cjthomas-opensource/sfx-boards/pcb-202009-9v/mech/drawings/sfx-9v-adapter.png

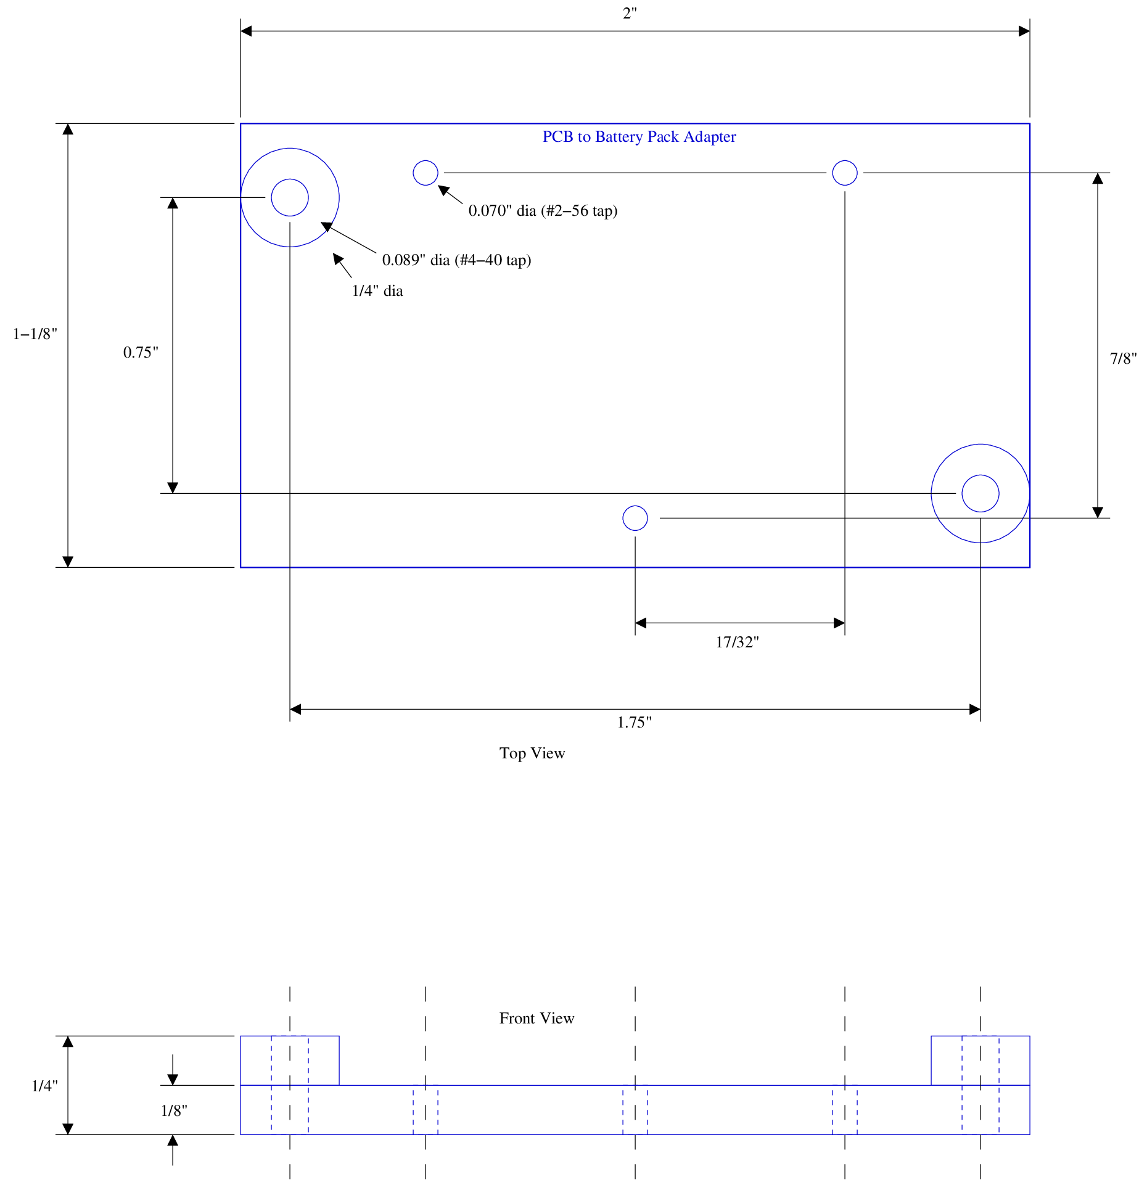
pcb-202009-9v/mech/drawings/sfx-9v-adapter.png
