cjthomas-opensource/sfx-boards/pcb-202009-9v/mech/drawings/sfx-9v-drawing.png

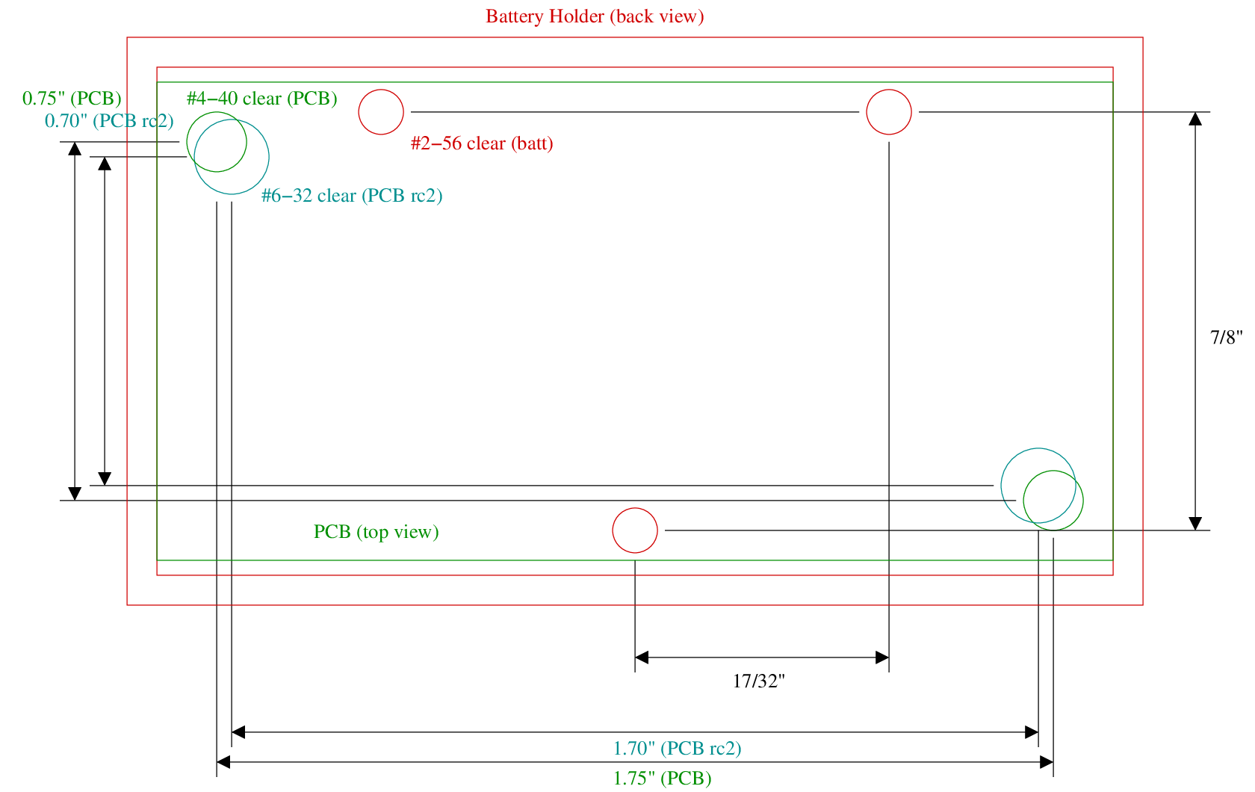
pcb-202009-9v/mech/drawings/sfx-9v-drawing.png
