cjthomas-opensource/sfx-boards/pcb-202009-9v/plots/sfx-9v-202009-rc1.png

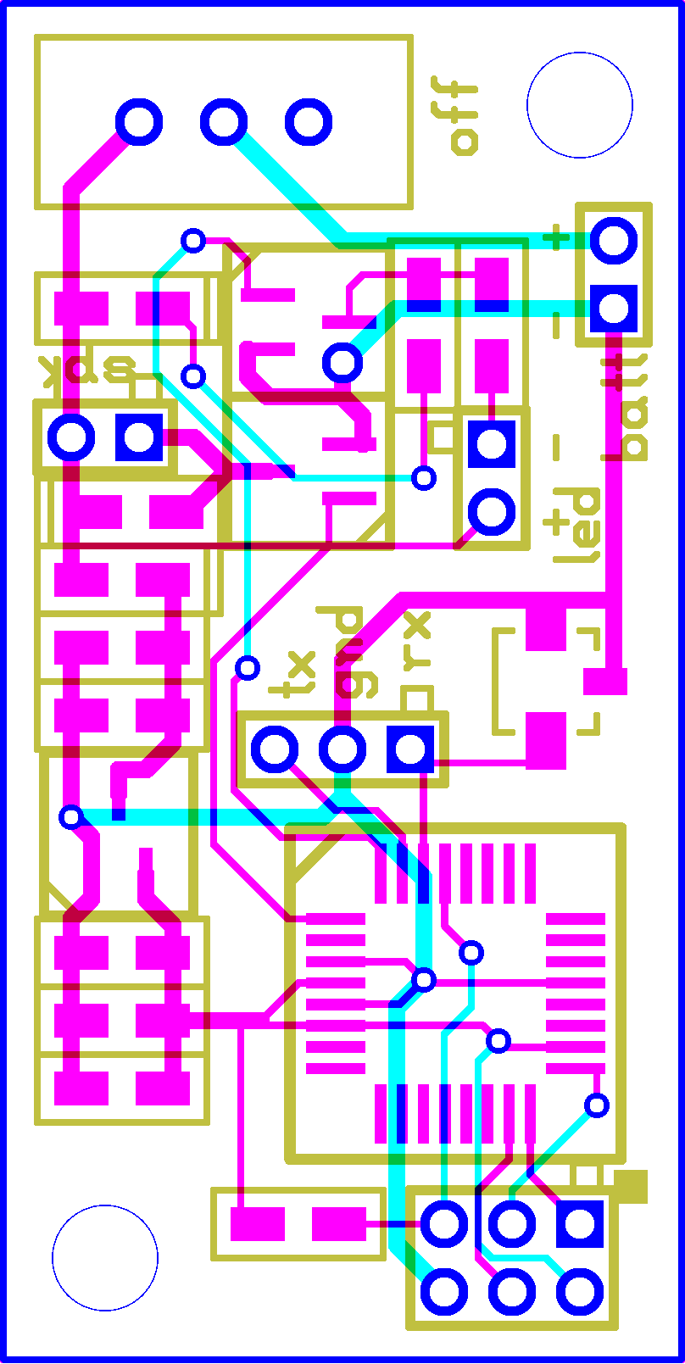
pcb-202009-9v/plots/sfx-9v-202009-rc1.png
