cjthomas-opensource/sfx-boards/pcb-202009-9v/plots/sfx-9v-202009-rc2-annotated.png

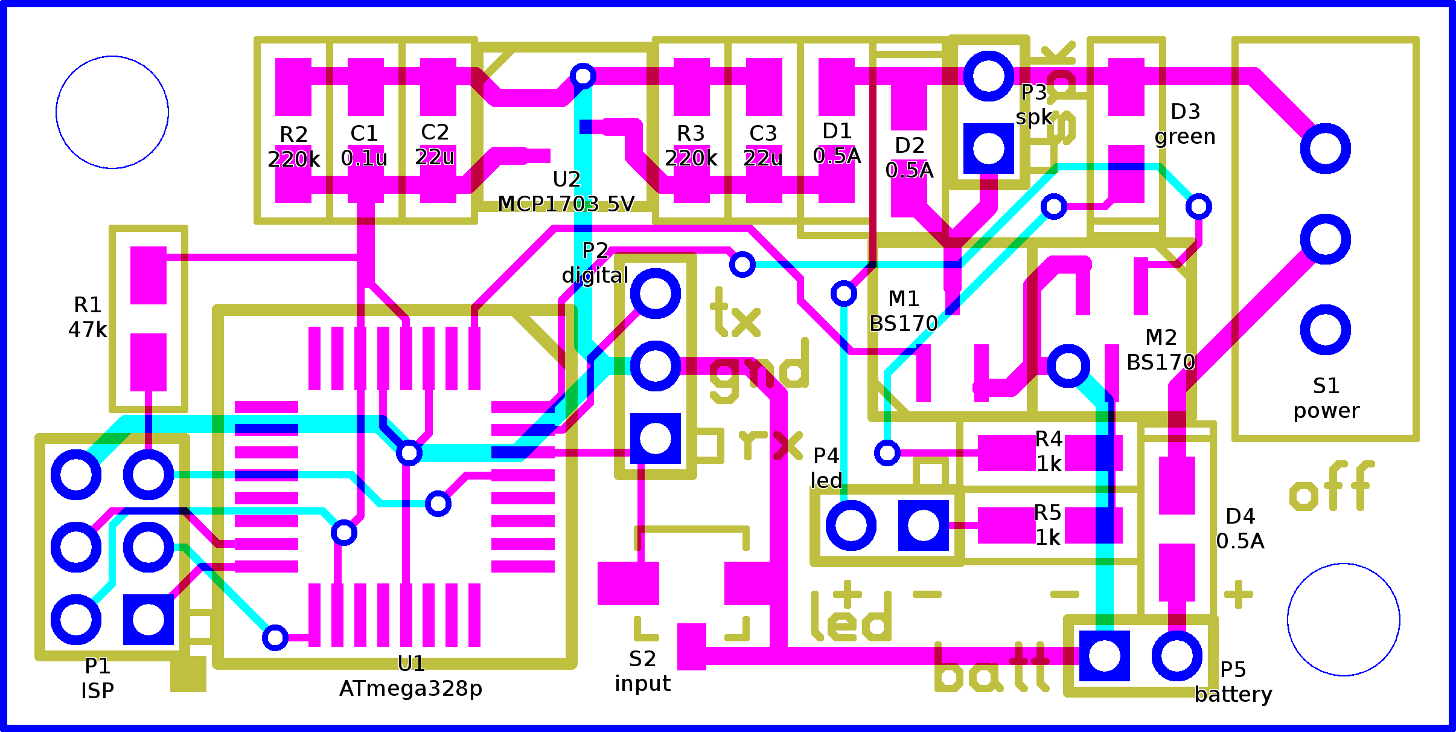
pcb-202009-9v/plots/sfx-9v-202009-rc2-annotated.png
