cjthomas-opensource/sfx-boards/pcb-202009-9v/plots/sfx-9v-202009-rc2.png

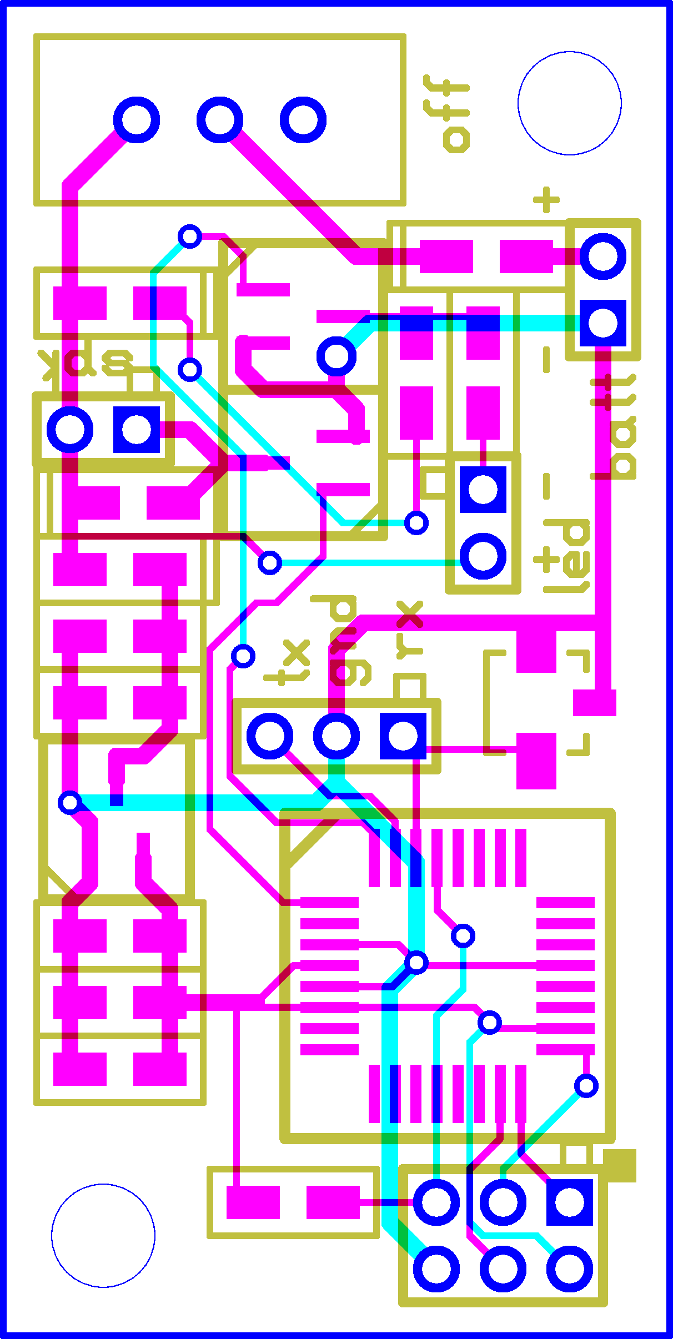
pcb-202009-9v/plots/sfx-9v-202009-rc2.png
