cjthomas-opensource/sfx-boards/vendor-datasheets/atmega328p-parallel-prog-pins.png

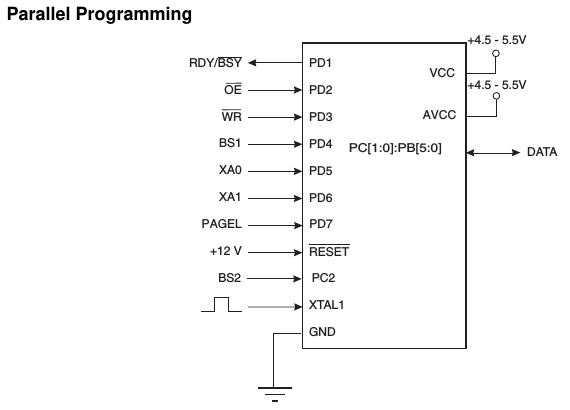
vendor-datasheets/atmega328p-parallel-prog-pins.png
