cjthomas-opensource/sfx-boards/vendor-datasheets/uno-schem.jpg

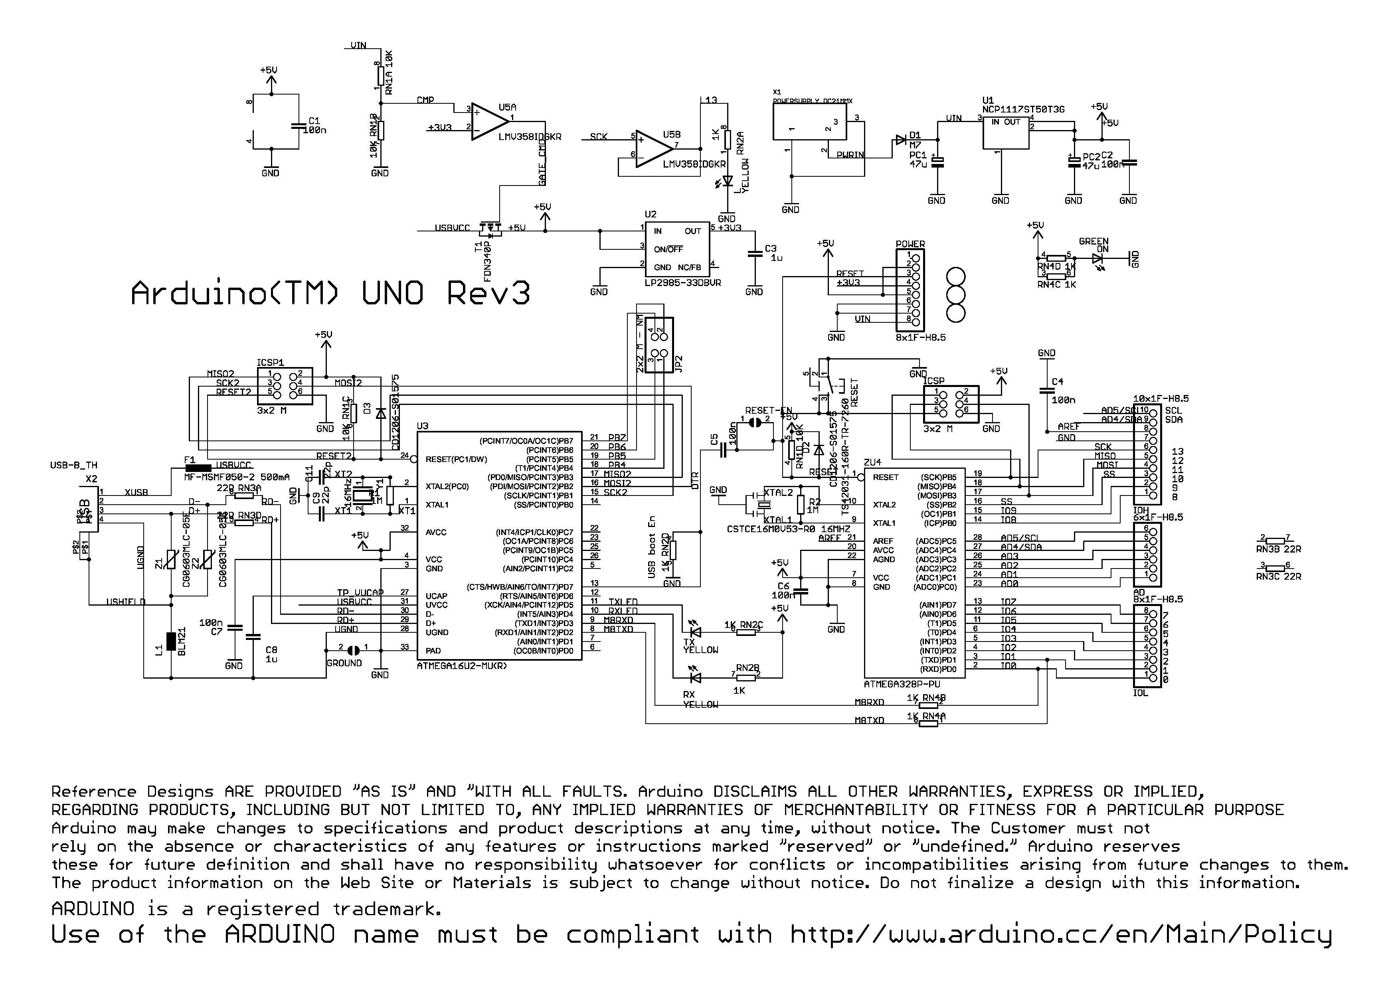
vendor-datasheets/uno-schem.jpg
